bsorgo/beegl/hw/3D_models/beegl_broker_solar_panel_holder_beegl_broker_mount.stl

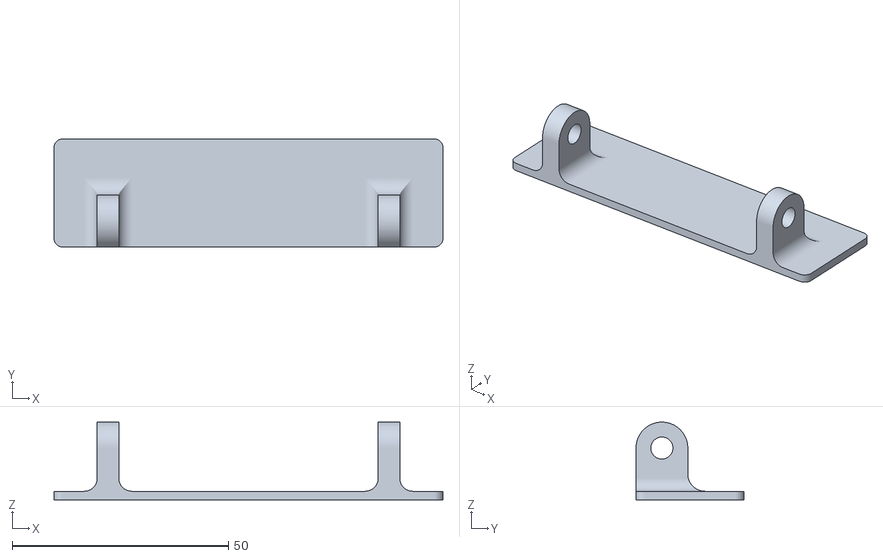
[picture p16: CAD file, 2019-08-28]
hw/3D_models/beegl_broker_solar_panel_holder_beegl_broker_mount.stl
90.0 x 25.0 x 18.0
