bsorgo/beegl/hw/3D_models/beegl_broker_variant_C_hx711_dht22_case.stl

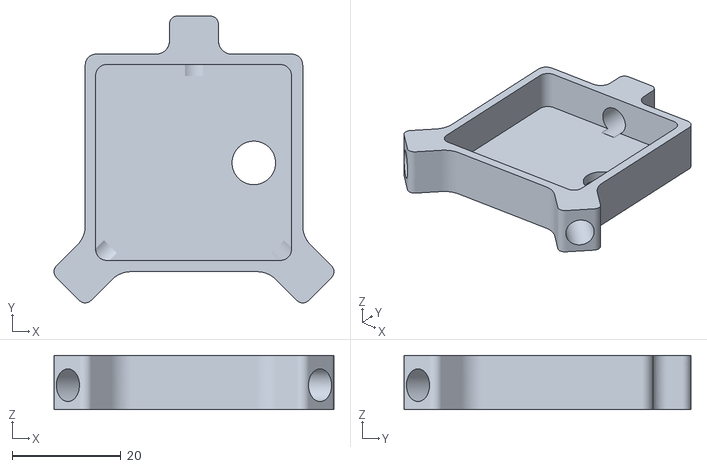
[picture p17: CAD file, 2019-08-28]
hw/3D_models/beegl_broker_variant_C_hx711_dht22_case.stl
51.5 x 52.7 x 10.0
