bsorgo/beegl/hw/3D_models/beegl_broker_variant_B_almgsi_20x20x2_straight_bar_load_cell_base.stl

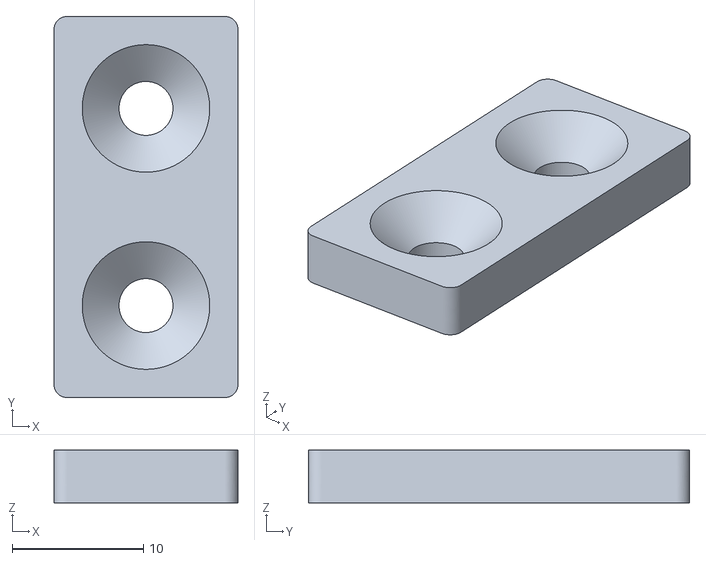
[picture p18: CAD file, 2019-08-28]
hw/3D_models/beegl_broker_variant_B_almgsi_20x20x2_straight_bar_load_cell_base.stl
14.0 x 29.0 x 4.00
