bsorgo/beegl/hw/3D_models/beegl_broker_variant_A_load_cell_holder.stl

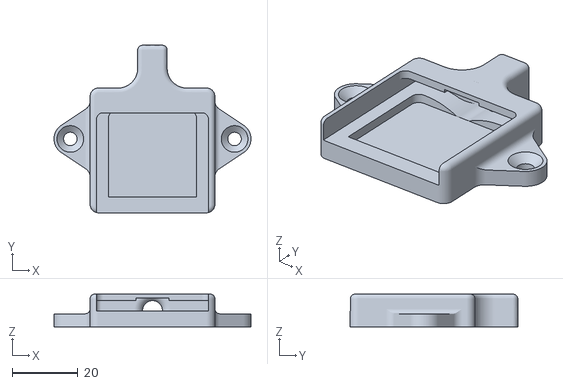
[picture p19: CAD file, 2019-08-28]
hw/3D_models/beegl_broker_variant_A_load_cell_holder.stl
60.0 x 51.1 x 10.0
